mniemela/PS2toSerial/avr/PS2toSerial/constants.h

/*
 * constants.h
 *
 * Created: 17.2.2026 22.03.12
 *  Author: Mikael Niemelä
 */ 


#ifndef CONSTANTS_H_
#define CONSTANTS_H_

#ifndef PS2_TX_BUF_SIZE
#define PS2_TX_BUF_SIZE 16
#endif

#ifndef TX_BUF_SIZE
#define TX_BUF_SIZE 32
#endif

#ifndef F_CPU
#define F_CPU 18432000
#endif


#endif /* CONSTANTS_H_ */
