mniemela/PS2toSerial/avr/PS2toSerial/ps2.h

/*
 * ps2.h
 *
 * Created: 4.1.2026 14.05.08
 *  Author: Mikael Niemelä
 */

#ifndef PS2_H_
#define PS2_H_

void ps2_init(uint8_t sampleRate_, uint8_t resolution_, uint8_t highSpeedUart_);
char getMouseType();
void resetMouse();


#endif /* PS2_H_ */
